OPIN-Smart-Home/ACControl/Casing/left.png

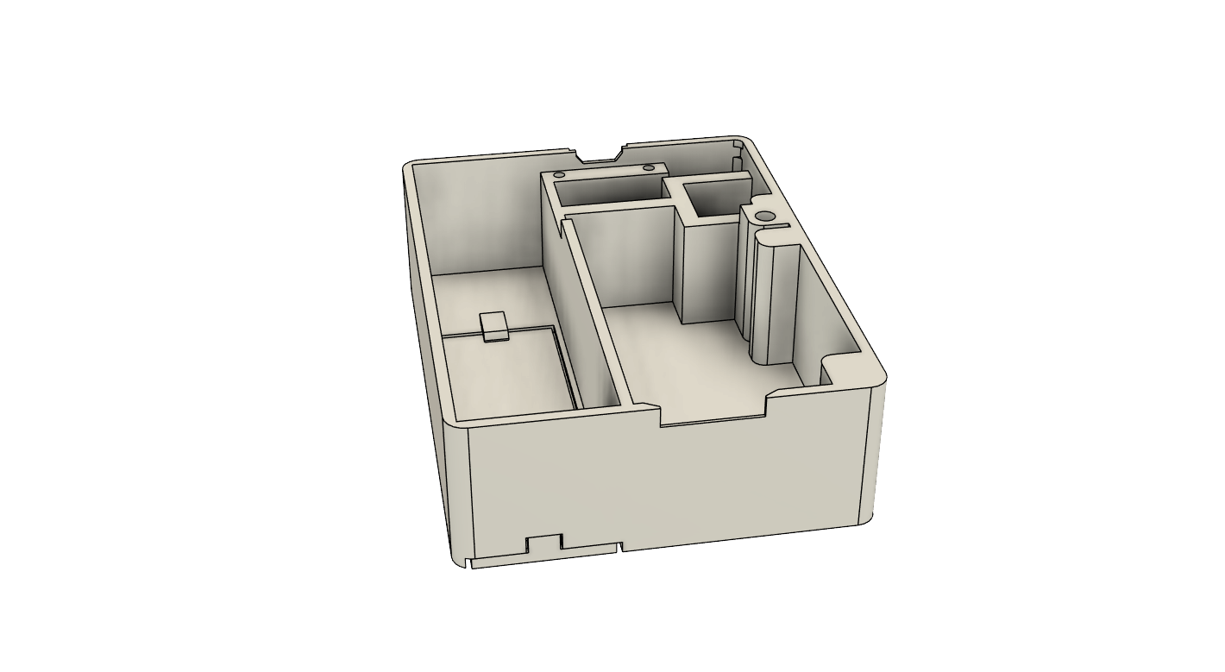
Casing/left.png
