OPIN-Smart-Home/ACControl/PCB/AC_controller_pcb.png

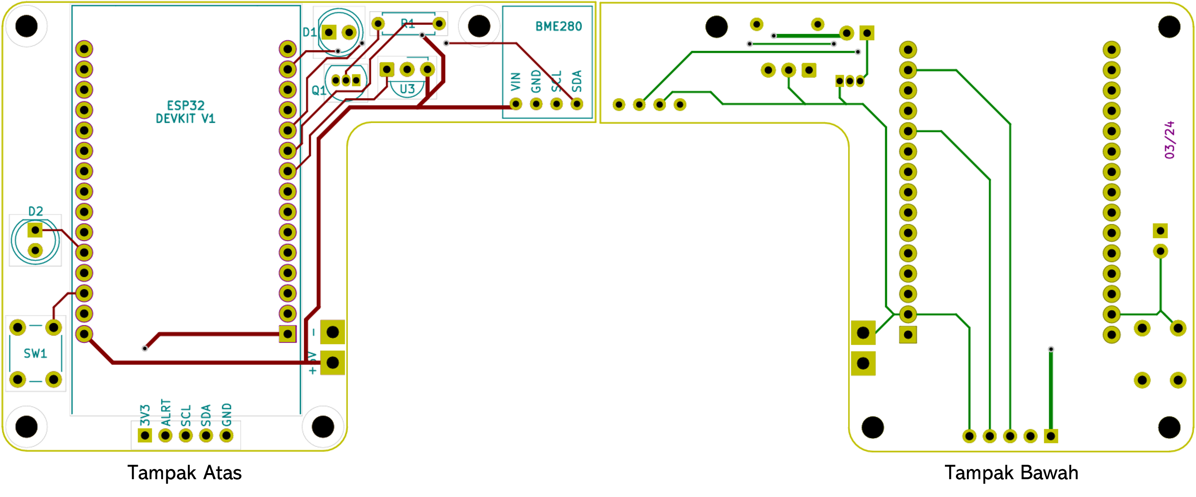
PCB/AC_controller_pcb.png
